leipopo/kekeandzuozuo4rock5b/stl/座座/屏幕盖.stl

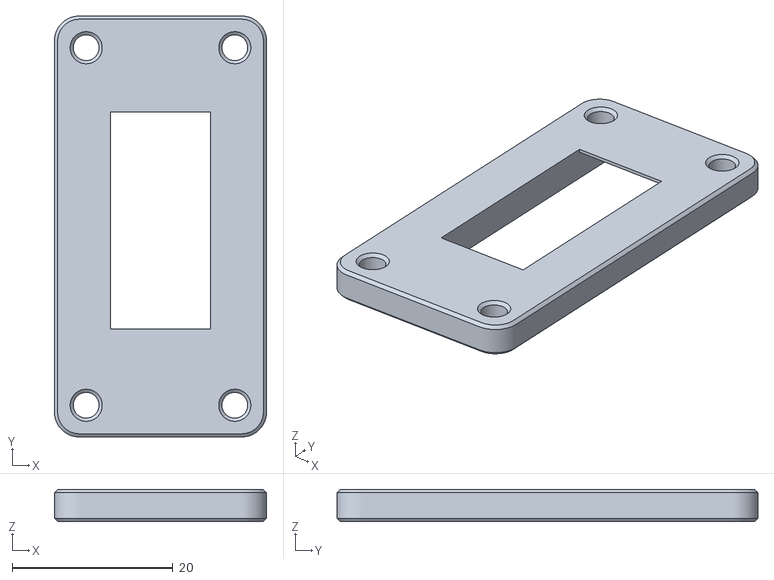
[picture p36: CAD file, 2022-11-09]
stl/座座/屏幕盖.stl
26.4 x 52.4 x 4.00
