leipopo/kekeandzuozuo4rock5b/stl/散热片散热/风扇座.stl

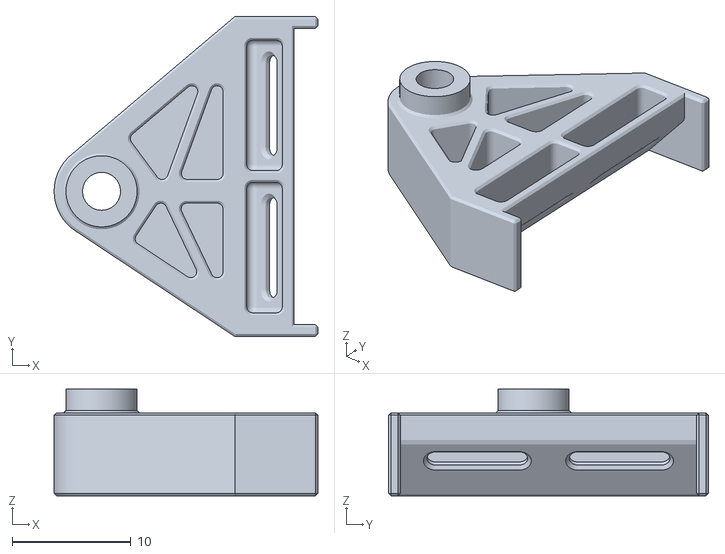
[picture p37: CAD file, 2022-11-09]
stl/散热片散热/风扇座.stl
22.2 x 27.0 x 9.00
