leipopo/kekeandzuozuo4rock5b/stl/壳壳基础打印件/改件/下框加高.stl

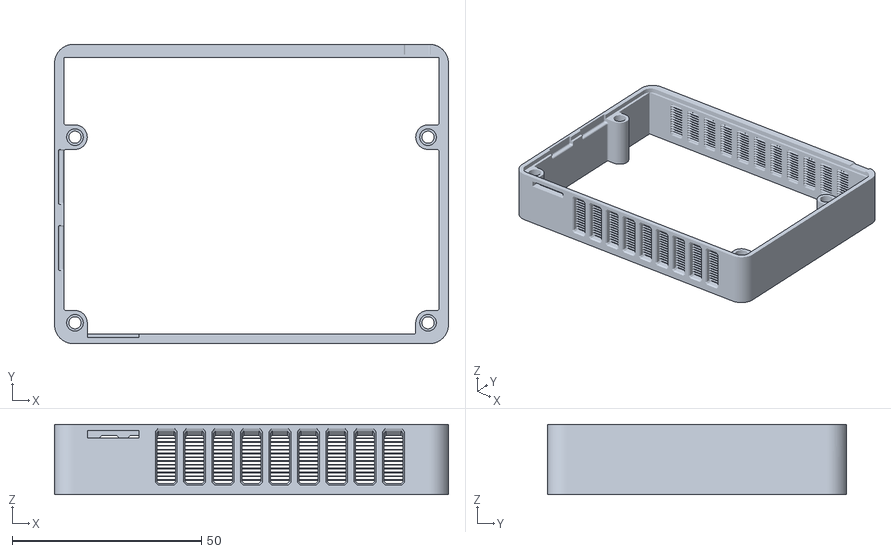
[picture p38: CAD file, 2022-12-31]
stl/壳壳基础打印件/改件/下框加高.stl
104.0 x 79.0 x 18.6
